feranick/Pi-bot/Utilities/i2c/test4.py

#!/usr/bin/env python3

# Simple demo of reading each analog input from the ADS1x15 and printing it to
# the screen.
# Author: Tony DiCola
# License: Public Domain
import time

# Import the ADS1x15 module.
import Adafruit_ADS1x15


# Create an ADS1115 ADC (16-bit) instance.
adc = Adafruit_ADS1x15.ADS1115(address=0x48,busnum=1)

# Or create an ADS1015 ADC (12-bit) instance.
#adc = Adafruit_ADS1x15.ADS1015()

# Note you can change the I2C address from its default (0x48), and/or the I2C
# bus by passing in these optional parameters:
#adc = Adafruit_ADS1x15.ADS1015(address=0x49, busnum=1)

# Choose a gain of 1 for reading voltages from 0 to 4.09V.
# Or pick a different gain to change the range of voltages that are read:
#  - 2/3 = +/-6.144V
#  -   1 = +/-4.096V
#  -   2 = +/-2.048V
#  -   4 = +/-1.024V
#  -   8 = +/-0.512V
#  -  16 = +/-0.256V
# See table 3 in the ADS1015/ADS1115 datasheet for more info on gain.
GAIN = 1
factor = 5/32768

print('Reading ADS1x15 values, press Ctrl-C to quit...')
# Print nice channel column headers.
print('| {0:>6} | {1:>6} | {2:>6} | {3:>6} |'.format(*range(4)))
print('-' * 37)
# Main loop.
while True:
    # Read all the ADC channel values in a list.
    values = [0]*4
    for i in range(4):
        # Read the specified ADC channel using the previously set gain value.
        values[i] = factor*adc.read_adc(i, gain=GAIN, data_rate=128)
        # Note you can also pass in an optional data_rate parameter that controls
        # the ADC conversion time (in samples/second). Each chip has a different
        # set of allowed data rate values, see datasheet Table 9 config register
        # DR bit values.
        #values[i] = adc.read_adc(i, gain=GAIN, data_rate=128)
        # Each value will be a 12 or 16 bit signed integer value depending on the
        # ADC (ADS1015 = 12-bit, ADS1115 = 16-bit).
    # Print the ADC values.
    print('| {0:.2f} | {1:.2f} | {2:.2f} | {3:.2f} |'.format(*values))
    # Pause for half a second.
    time.sleep(0.5)
